taylorswift22/dimension1800/dimension-PCB/dimension-PCB.kicad_sch

## KiCad design dimension-PCB/dimension-PCB.kicad_sch (2024-06-22)

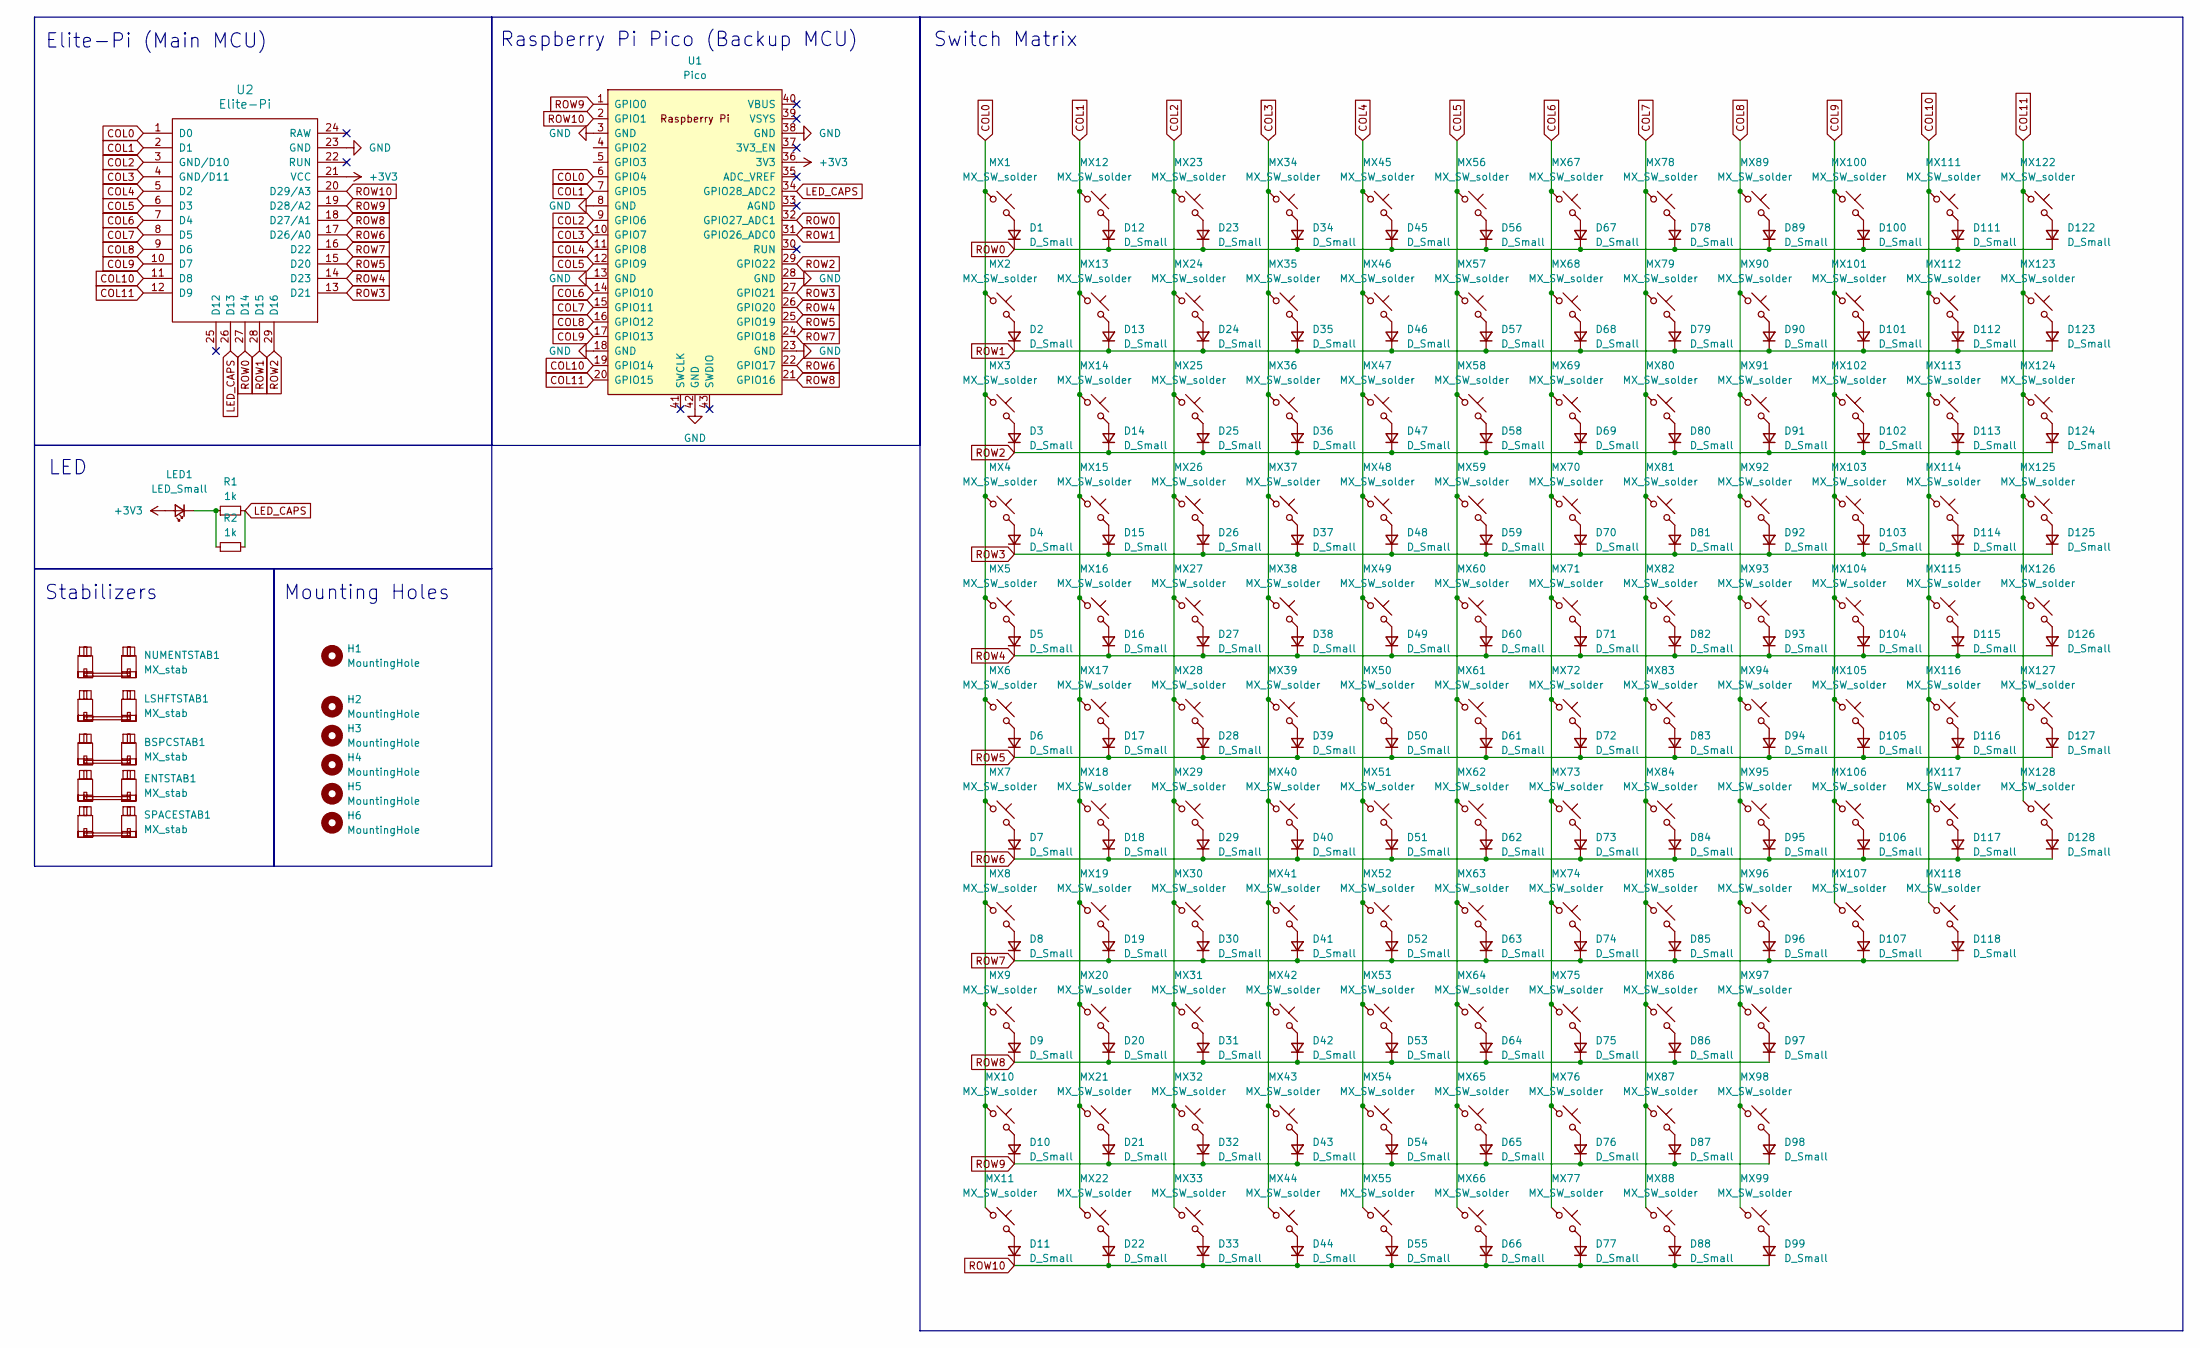
[picture p2: schematic dimension-PCB.kicad_sch]

Parts:
BSPCSTAB1: MX_stab; STAB_MX_P_2u
D1, D2, D3, D4, D5, D6, D7, D8, D9, D10, D11, D12, D13, D14, D15, D16, D17, D18, D19, D20, D21, D22, D23, D24, D25, D26, D27, D28, D29, D30, D31, D32, D33, D34, D35, D36, D37, D38, D39, D40, D41, D42, D43, D44, D45, D46, D47, D48, D49, D50, D51, D52, D53, D54, D55, D56, D57, D58, D59, D60, D61, D62, D63, D64, D65, D66, D67, D68, D69, D70, D71, D72, D73, D74, D75, D76, D77, D78, D79, D80, D81, D82, D83, D84, D85, D86, D87, D88, D89, D90, D91, D92, D93, D94, D95, D96, D97, D98, D99, D100, D101, D102, D103, D104, D105, D106, D107, D111, D112, D113, D114, D115, D116, D117, D118, D122, D123, D124, D125, D126, D127, D128: D_Small; D_SOD-123_THT_COMBO
ENTSTAB1: MX_stab; STAB_MX_P_2u
H1: MountingHole; MountingHole_8.4mm_M8
H2, H3, H4, H5, H6: MountingHole; MountingHole_4.3mm_M4
LED1: LED_Small; LED_D3.0mm
LSHFTSTAB1: MX_stab; STAB_MX_P_2u
MX1, MX2, MX3, MX4, MX5, MX6, MX7, MX8, MX9, MX10, MX11, MX12, MX13, MX14, MX15, MX16, MX17, MX18, MX19, MX20, MX21, MX22, MX23, MX24, MX25, MX26, MX27, MX28, MX29, MX30, MX31, MX32, MX33, MX34, MX35, MX36, MX37, MX38, MX39, MX40, MX41, MX42, MX43, MX44, MX45, MX46, MX47, MX48, MX49, MX50, MX51, MX52, MX53, MX54, MX55, MX56, MX57, MX58, MX59, MX60, MX61, MX62, MX63, MX64, MX65, MX66, MX67, MX68, MX69, MX70, MX71, MX72, MX73, MX74, MX75, MX76, MX77, MX78, MX79, MX80, MX81, MX82, MX83, MX84, MX85, MX86, MX87, MX88, MX89, MX90, MX91, MX92, MX93, MX94, MX95, MX96, MX97, MX98, MX99, MX100, MX101, MX102, MX103, MX104, MX105, MX106, MX107, MX111, MX112, MX113, MX114, MX115, MX116, MX117, MX118, MX122, MX123, MX124, MX125, MX126, MX127, MX128: MX_SW_solder; SW_MX_1u
NUMENTSTAB1: MX_stab; STAB_MX_P_2u
R1: 1k; R_0603_1608Metric
R2: 1k; R_Axial_DIN0207_L6.3mm_D2.5mm_P7.62mm_Horizontal
SPACESTAB1: MX_stab; STAB_MX_7u_SPPBTDCS
U1: Pico; RPi_Pico_SMD_TH
U2: Elite-Pi

Connections:
+3V3: LED1.2 (A), U1.36 (3V3), U2.21 (VCC)
COL0: MX1.1, MX2.1, MX3.1, MX4.1, MX5.1, MX6.1, MX7.1, MX8.1, MX9.1, MX10.1, MX11.1, U1.6 (GPIO4), U2.1 (D0)
COL1: MX12.1, MX13.1, MX14.1, MX15.1, MX16.1, MX17.1, MX18.1, MX19.1, MX20.1, MX21.1, MX22.1, U1.7 (GPIO5), U2.2 (D1)
COL2: MX23.1, MX24.1, MX25.1, MX26.1, MX27.1, MX28.1, MX29.1, MX30.1, MX31.1, MX32.1, MX33.1, U1.9 (GPIO6), U2.3 (GND/D10)
COL3: MX34.1, MX35.1, MX36.1, MX37.1, MX38.1, MX39.1, MX40.1, MX41.1, MX42.1, MX43.1, MX44.1, U1.10 (GPIO7), U2.4 (GND/D11)
COL4: MX45.1, MX46.1, MX47.1, MX48.1, MX49.1, MX50.1, MX51.1, MX52.1, MX53.1, MX54.1, MX55.1, U1.11 (GPIO8), U2.5 (D2)
COL5: MX56.1, MX57.1, MX58.1, MX59.1, MX60.1, MX61.1, MX62.1, MX63.1, MX64.1, MX65.1, MX66.1, U1.12 (GPIO9), U2.6 (D3)
COL6: MX67.1, MX68.1, MX69.1, MX70.1, MX71.1, MX72.1, MX73.1, MX74.1, MX75.1, MX76.1, MX77.1, U1.14 (GPIO10), U2.7 (D4)
COL7: MX78.1, MX79.1, MX80.1, MX81.1, MX82.1, MX83.1, MX84.1, MX85.1, MX86.1, MX87.1, MX88.1, U1.15 (GPIO11), U2.8 (D5)
COL8: MX89.1, MX90.1, MX91.1, MX92.1, MX93.1, MX94.1, MX95.1, MX96.1, MX97.1, MX98.1, MX99.1, U1.16 (GPIO12), U2.9 (D6)
COL9: MX100.1, MX101.1, MX102.1, MX103.1, MX104.1, MX105.1, MX106.1, MX107.1, U1.17 (GPIO13), U2.10 (D7)
COL10: MX111.1, MX112.1, MX113.1, MX114.1, MX115.1, MX116.1, MX117.1, MX118.1, U1.19 (GPIO14), U2.11 (D8)
COL11: MX122.1, MX123.1, MX124.1, MX125.1, MX126.1, MX127.1, MX128.1, U1.20 (GPIO15), U2.12 (D9)
GND: U1.3 (GND), U1.8 (GND), U1.13 (GND), U1.18 (GND), U1.23 (GND), U1.28 (GND), U1.38 (GND), U1.42 (GND), U2.23 (GND)
LED_CAPS: R1.2, R2.2, U1.34 (GPIO28_ADC2), U2.26 (D13)
unnamed: D1.2 (A), MX1.2
unnamed: D2.2 (A), MX2.2
unnamed: D3.2 (A), MX3.2
unnamed: D4.2 (A), MX4.2
unnamed: D5.2 (A), MX5.2
unnamed: D6.2 (A), MX6.2
unnamed: D7.2 (A), MX7.2
unnamed: D8.2 (A), MX8.2
unnamed: D9.2 (A), MX9.2
unnamed: D10.2 (A), MX10.2
unnamed: D11.2 (A), MX11.2
unnamed: D12.2 (A), MX12.2
unnamed: D13.2 (A), MX13.2
unnamed: D14.2 (A), MX14.2
unnamed: D15.2 (A), MX15.2
unnamed: D16.2 (A), MX16.2
unnamed: D17.2 (A), MX17.2
unnamed: D18.2 (A), MX18.2
unnamed: D19.2 (A), MX19.2
unnamed: D20.2 (A), MX20.2
unnamed: D21.2 (A), MX21.2
unnamed: D22.2 (A), MX22.2
unnamed: D23.2 (A), MX23.2
unnamed: D24.2 (A), MX24.2
unnamed: D25.2 (A), MX25.2
unnamed: D26.2 (A), MX26.2
unnamed: D27.2 (A), MX27.2
unnamed: D28.2 (A), MX28.2
unnamed: D29.2 (A), MX29.2
unnamed: D30.2 (A), MX30.2
unnamed: D31.2 (A), MX31.2
unnamed: D32.2 (A), MX32.2
unnamed: D33.2 (A), MX33.2
unnamed: D34.2 (A), MX34.2
unnamed: D35.2 (A), MX35.2
unnamed: D36.2 (A), MX36.2
unnamed: D37.2 (A), MX37.2
unnamed: D38.2 (A), MX38.2
unnamed: D39.2 (A), MX39.2
unnamed: D40.2 (A), MX40.2
unnamed: D41.2 (A), MX41.2
unnamed: D42.2 (A), MX42.2
unnamed: D43.2 (A), MX43.2
unnamed: D44.2 (A), MX44.2
unnamed: D45.2 (A), MX45.2
unnamed: D46.2 (A), MX46.2
unnamed: D47.2 (A), MX47.2
unnamed: D48.2 (A), MX48.2
unnamed: D49.2 (A), MX49.2
unnamed: D50.2 (A), MX50.2
unnamed: D51.2 (A), MX51.2
unnamed: D52.2 (A), MX52.2
unnamed: D53.2 (A), MX53.2
unnamed: D54.2 (A), MX54.2
unnamed: D55.2 (A), MX55.2
unnamed: D56.2 (A), MX56.2
unnamed: D57.2 (A), MX57.2
unnamed: D58.2 (A), MX58.2
unnamed: D59.2 (A), MX59.2
unnamed: D60.2 (A), MX60.2
unnamed: D61.2 (A), MX61.2
unnamed: D62.2 (A), MX62.2
unnamed: D63.2 (A), MX63.2
unnamed: D64.2 (A), MX64.2
unnamed: D65.2 (A), MX65.2
unnamed: D66.2 (A), MX66.2
unnamed: D67.2 (A), MX67.2
unnamed: D68.2 (A), MX68.2
unnamed: D69.2 (A), MX69.2
unnamed: D70.2 (A), MX70.2
unnamed: D71.2 (A), MX71.2
unnamed: D72.2 (A), MX72.2
unnamed: D73.2 (A), MX73.2
unnamed: D74.2 (A), MX74.2
unnamed: D75.2 (A), MX75.2
unnamed: D76.2 (A), MX76.2
unnamed: D77.2 (A), MX77.2
unnamed: D78.2 (A), MX78.2
unnamed: D79.2 (A), MX79.2
unnamed: D80.2 (A), MX80.2
unnamed: D81.2 (A), MX81.2
unnamed: D82.2 (A), MX82.2
unnamed: D83.2 (A), MX83.2
unnamed: D84.2 (A), MX84.2
unnamed: D85.2 (A), MX85.2
unnamed: D86.2 (A), MX86.2
unnamed: D87.2 (A), MX87.2
unnamed: D88.2 (A), MX88.2
unnamed: D89.2 (A), MX89.2
unnamed: D90.2 (A), MX90.2
unnamed: D91.2 (A), MX91.2
unnamed: D92.2 (A), MX92.2
unnamed: D93.2 (A), MX93.2
unnamed: D94.2 (A), MX94.2
unnamed: D95.2 (A), MX95.2
unnamed: D96.2 (A), MX96.2
unnamed: D97.2 (A), MX97.2
unnamed: D98.2 (A), MX98.2
unnamed: D99.2 (A), MX99.2
unnamed: D100.2 (A), MX100.2
unnamed: D101.2 (A), MX101.2
unnamed: D102.2 (A), MX102.2
unnamed: D103.2 (A), MX103.2
unnamed: D104.2 (A), MX104.2
unnamed: D105.2 (A), MX105.2
unnamed: D106.2 (A), MX106.2
unnamed: D107.2 (A), MX107.2
unnamed: D111.2 (A), MX111.2
unnamed: D112.2 (A), MX112.2
unnamed: D113.2 (A), MX113.2
unnamed: D114.2 (A), MX114.2
unnamed: D115.2 (A), MX115.2
unnamed: D116.2 (A), MX116.2
unnamed: D117.2 (A), MX117.2
unnamed: D118.2 (A), MX118.2
unnamed: D122.2 (A), MX122.2
unnamed: D123.2 (A), MX123.2
unnamed: D124.2 (A), MX124.2
unnamed: D125.2 (A), MX125.2
unnamed: D126.2 (A), MX126.2
unnamed: D127.2 (A), MX127.2
unnamed: D128.2 (A), MX128.2
unnamed: LED1.1 (K), R1.1, R2.1
ROW0: D1.1 (K), D12.1 (K), D23.1 (K), D34.1 (K), D45.1 (K), D56.1 (K), D67.1 (K), D78.1 (K), D89.1 (K), D100.1 (K), D111.1 (K), D122.1 (K), U1.32 (GPIO27_ADC1), U2.27 (D14)
ROW1: D2.1 (K), D13.1 (K), D24.1 (K), D35.1 (K), D46.1 (K), D57.1 (K), D68.1 (K), D79.1 (K), D90.1 (K), D101.1 (K), D112.1 (K), D123.1 (K), U1.31 (GPIO26_ADC0), U2.28 (D15)
ROW2: D3.1 (K), D14.1 (K), D25.1 (K), D36.1 (K), D47.1 (K), D58.1 (K), D69.1 (K), D80.1 (K), D91.1 (K), D102.1 (K), D113.1 (K), D124.1 (K), U1.29 (GPIO22), U2.29 (D16)
ROW3: D4.1 (K), D15.1 (K), D26.1 (K), D37.1 (K), D48.1 (K), D59.1 (K), D70.1 (K), D81.1 (K), D92.1 (K), D103.1 (K), D114.1 (K), D125.1 (K), U1.27 (GPIO21), U2.13 (D21)
ROW4: D5.1 (K), D16.1 (K), D27.1 (K), D38.1 (K), D49.1 (K), D60.1 (K), D71.1 (K), D82.1 (K), D93.1 (K), D104.1 (K), D115.1 (K), D126.1 (K), U1.26 (GPIO20), U2.14 (D23)
ROW5: D6.1 (K), D17.1 (K), D28.1 (K), D39.1 (K), D50.1 (K), D61.1 (K), D72.1 (K), D83.1 (K), D94.1 (K), D105.1 (K), D116.1 (K), D127.1 (K), U1.25 (GPIO19), U2.15 (D20)
ROW6: D7.1 (K), D18.1 (K), D29.1 (K), D40.1 (K), D51.1 (K), D62.1 (K), D73.1 (K), D84.1 (K), D95.1 (K), D106.1 (K), D117.1 (K), D128.1 (K), U1.22 (GPIO17), U2.17 (D26/A0)
ROW7: D8.1 (K), D19.1 (K), D30.1 (K), D41.1 (K), D52.1 (K), D63.1 (K), D74.1 (K), D85.1 (K), D96.1 (K), D107.1 (K), D118.1 (K), U1.24 (GPIO18), U2.16 (D22)
ROW8: D9.1 (K), D20.1 (K), D31.1 (K), D42.1 (K), D53.1 (K), D64.1 (K), D75.1 (K), D86.1 (K), D97.1 (K), U1.21 (GPIO16), U2.18 (D27/A1)
ROW9: D10.1 (K), D21.1 (K), D32.1 (K), D43.1 (K), D54.1 (K), D65.1 (K), D76.1 (K), D87.1 (K), D98.1 (K), U1.1 (GPIO0), U2.19 (D28/A2)
ROW10: D11.1 (K), D22.1 (K), D33.1 (K), D44.1 (K), D55.1 (K), D66.1 (K), D77.1 (K), D88.1 (K), D99.1 (K), U1.2 (GPIO1), U2.20 (D29/A3)

Notes on the sheet:
Stabilizers
Switch Matrix
LED
Raspberry Pi Pico (Backup MCU)
Elite-Pi (Main MCU)
Mounting Holes
